dracir9/3DPrinterScreen/main/Menu/preview_Scr.cpp

/**
 * @file   gcodePreview_Scr.cpp
 * @author Ricard Bitriá Ribes (https://github.com/dracir9)
 * Created Date: 22-01-2022
 * -----
 * Last Modified: 10-04-2023
 * Modified By: Ricard Bitriá Ribes
 * -----
 * @copyright (c) 2022 Ricard Bitriá Ribes
 * 
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
 * You should have received a copy of the GNU General Public License
 * along with this program.  If not, see <https://www.gnu.org/licenses/>.
 */

#include "preview_Scr.h"
#include "dbg_log.h"

Preview_Scr::Preview_Scr(lcdUI* UI, tftLCD& tft, TchScr_Drv& ts):
    Screen(UI)
{
    renderEngine = GCodeRenderer::instance();
    if (renderEngine == nullptr)
        DBG_LOGE("Render engine uninitialized!");

    displayed.reset();
    tft.drawRoundRect(320, 0, 160, 50, 4, TFT_BLUE);
    tft.drawRoundRect(0, 0, 320, 320, 4, TFT_GREEN);
    tft.drawRoundRect(320, 270, 160, 50, 4, TFT_ORANGE);
    tft.setTextFont(2);
    tft.setTextSize(1);
    tft.setTextDatum(CC_DATUM);
    tft.setTextPadding(0);
    tft.drawStringWr(_UI->getFile().substr(_UI->getFile().rfind('/')+1).c_str(), 400, 25, 150, 48); // Display filename
    tft.setTextColor(TFT_WHITE);
    tft.drawString("Loading...", 160, 152);
    tft.drawBmpSPIFFS("/spiffs/return_48.bmp", 376, 277);

    if (printer->getState() == READY)
    {
        tft.fillRoundRect(320, 220, 160, 50, 4, TFT_OLIVE);
        tft.drawString("Start!", 400, 245);
        printerReady = true;
    }
    else
    {
        tft.fillRoundRect(320, 220, 160, 50, 4, TFT_DARKGREY);
        tft.drawString("Printer disconnected", 400, 245);
        printerReady = false;
    }

    // Setup buttons
    Button tmpBut;
    tmpBut.id = 0;
    tmpBut.xmin = 320;
    tmpBut.xmax = 480;
    tmpBut.ymin = 270;
    tmpBut.ymax = 320;
    tmpBut.enReleaseEv = true;
    
    ts.setButton(&tmpBut); // Back to Info screen

    tmpBut.id = 1;
    tmpBut.xmin = 320;
    tmpBut.xmax = 480;
    tmpBut.ymin = 220;
    tmpBut.ymax = 270;
    
    ts.setButton(&tmpBut); // Start button
}

void Preview_Scr::update(const uint32_t deltaTime, TchScr_Drv& ts)
{
    if (!started)
    {
        if (renderEngine->begin(_UI->getFile().c_str()) == ESP_OK)
            started = true;
        else
            _UI->requestUpdate();
    }

    if (!_UI->isSDinit())
    {
        _UI->setScreen(lcdUI::INFO_SCR);
    }
}

void Preview_Scr::render(tftLCD& tft)
{
    _UI->requestUpdate();

    tft.setTextFont(2);
    tft.setTextSize(1);
    tft.setTextDatum(CC_DATUM);
    tft.setTextPadding(0);
    tft.setTextColor(TFT_WHITE);
    if (printer->getState() == READY && printerReady == false)
    {
        tft.fillRoundRect(320, 220, 160, 50, 4, TFT_OLIVE);
        tft.drawString("Start!", 400, 245);
        printerReady = true;
    }
    else if (printer->getState() != READY && printerReady == true)
    {
        tft.fillRoundRect(320, 220, 160, 50, 4, TFT_DARKGREY);
        tft.drawString("Printer disconnected", 400, 245);
    }

    if (rendered) return;
    uint16_t* img = nullptr;
    // Main update loop is paused here
    esp_err_t ret = renderEngine->getRender(&img, pdMS_TO_TICKS(100));
    if (ret == ESP_OK)
    {
        bool oldBytes = tft.getSwapBytes();
        tft.setSwapBytes(true);
        tft.pushImage(0, 0, 320, 320, img);
        tft.setSwapBytes(oldBytes);
        tft.drawRoundRect(0, 0, 320, 320, 4, TFT_GREEN);
        rendered = true;
    }
    else if (ret == ESP_FAIL)
    {
        tft.setTextDatum(CC_DATUM);
        tft.setTextFont(4);
        tft.setTextSize(1);
        tft.setTextPadding(150);
        tft.setTextColor(TFT_WHITE, TFT_RED);
        tft.drawString("Render error", 160, 160);
        rendered = true;
    }

    drawInfo(tft);
}

void Preview_Scr::handleTouch(const TchEvent& event)
{
    if (event.trigger != TrgSrc::RELEASE) return;

    if (event.id == 0)
    {
        _UI->clearFile();
        _UI->setScreen(lcdUI::FILE_BROWSER_SRC);
    }
    else if (event.id == 1 && printer->getState() == PState::READY)
    {
        _UI->setScreen(lcdUI::PRINT_SCR);
    }
}

void Preview_Scr::drawInfo(tftLCD& tft)
{
    // Text settings
    tft.setTextDatum(TL_DATUM);
    tft.setTextFont(2);
    tft.setTextSize(1);
    tft.setTextPadding(0);
    tft.setTextColor(TFT_WHITE);
    String txt;

    const FileInfo* info = renderEngine->getInfo();

    if (info->filamentReady && !displayed[0])
    {
        tft.drawString("Filament cost: " , 328, 55);
        txt = String(info->filament, 3) + " m";
        tft.drawString(txt, 335, 71);
        displayed[0] = true;
    }

    if (info->timeReady && !displayed[1])
    {
        tft.drawString("Estimated time: " , 328, 95);
        int16_t seconds = info->printTime % 60;
        int16_t minutes = info->printTime/60 % 60;
        int16_t hours = info->printTime/3600 % 24;
        int16_t days = info->printTime/86400;
        txt = "";
        if (days > 0) txt += String(days) + "d ";
        if (hours > 0) txt += String(hours) + "h ";
        if (minutes > 0) txt += String(minutes) + "min ";
        txt += String(seconds) + "s";
        tft.drawString(txt, 335, 111);
        displayed[1] = true;
    }

    if (!rendered)
    {
        tft.setTextDatum(CC_DATUM);
        tft.setTextColor(TFT_WHITE, TFT_BLACK);
        tft.drawString(String(renderEngine->getProgress(), 0) + String("%"), 160, 168);
    }
}
